mugi111/STM32F4-MotherBoard_5.0.0/RCsemiSTM32F4_Ver500/RCsemiSTM32F4_Ver500/src/motherboard.cpp

/*
 * motherboard.cpp
 *
 *  Created on: 2017/04/19
 *      Author: mugi111
 */

#include <stm32f4xx_hal.h>
#include <stm32f4xx_hal_rcc.h>
#include <stm32f4xx_hal_gpio.h>
#include "motherboard.h"

namespace RCsemi{

motherboard::LED::LED()
{

}

void motherboard::LED::TurnOff()
{

}

void motherboard::LED::TurnOn()
{

}

void motherboard::LED::Toggle()
{

}

motherboard::PushSW::PushSW()
{

}

int motherboard::PushSW::isPushed()
{

	return 0;
}

motherboard::RotarySW::RotarySW()
{

}

unsigned int motherboard::RotarySW::Check()
{

	return 0;
}

}
