mugi111/STM32F4-MotherBoard_5.0.0/RCsemiSTM32F4_Ver500/RCsemiSTM32F4_Ver500/inc/motherboard.h

/*
 * motherboard.h
 *
 *  Created on: 2017/04/19
 *      Author: mugi111
 */

#ifndef MOTHERBOARD_H_
#define MOTHERBOARD_H_

namespace RCsemi{
class motherboard{
public:
	class LED{
		LED();

		void TurnOff();
		void TurnOn();
		void Toggle();
	};

	class PushSW{
		PushSW();

		int isPushed();
	};

	class RotarySW{
		RotarySW();

		unsigned int Check();
	};


};/* end class */

}/* end namespace */

#endif /* MOTHERBOARD_H_ */
